Sl-Alex/SmartWatch/FW/hw/src/sm_hw_battery.cpp

/**
    @file sm_hw_battery.cpp
*/
#include "sm_hw_battery.h"

#ifndef PC_SOFTWARE
#include "stm32f10x.h"
#include "sm_hal_gpio.h"

#define GPIO_EN_PORT    GPIOA_BASE  ///< Battery measurement enable port
#define GPIO_EN_PIN     2           ///< Battery measurement enable pin
#define GPIO_ST_PORT    GPIOA_BASE  ///< Charge status port
#define GPIO_ST_PIN     15          ///< Charge status pin
#define MEAS_DELAY      5           ///< Delay between enabling and measurement
#define MEAS_INTERVAL   500         ///< Battery voltage update interval

#define GPIO_AIN_PORT   GPIOA_BASE  ///< Battery voltage input port
#define GPIO_AIN_PIN    0           ///< Battery voltage input pin
#endif

#define VREF    3300                ///< ADC Reference voltage (mV)
#define VOLT_MAX 4100               ///< Maximum battery voltage
#define VOLT_MIN 3500               ///< Minimum battery voltage

#define BAT_MAX ((VOLT_MAX/2)*4096/VREF)    ///< Maximum raw ADC battery voltage
#define BAT_MIN ((VOLT_MIN/2)*4096/VREF)    ///< Minimum raw ADC battery voltage

void SmHwBattery::init()
{
    mRaw = 0;

#ifndef PC_SOFTWARE
    mGpioEn = new SmHalGpio<GPIO_EN_PORT, GPIO_EN_PIN>();
    mGpioEn->setModeSpeed(SM_HAL_GPIO_MODE_OUT_PP, SM_HAL_GPIO_SPEED_2M);
    mGpioEn->setPin();

    // When the charge is
    // in progress this pin is pulled low instead at the end of the charge cycle, a weak pull down of
    // approximately 20µA is connected to the CHRG pin, indicating a present supply power; if the
    // flag is forced high impedance an under voltage condition is detected.
    mGpioStatus = new SmHalGpio<GPIO_ST_PORT, GPIO_ST_PIN>();
    mGpioStatus->setModeSpeed(SM_HAL_GPIO_MODE_IN_PU, SM_HAL_GPIO_SPEED_2M);

    SmHalGpio<GPIO_AIN_PORT, GPIO_AIN_PIN> BatGpio;
    BatGpio.setModeSpeed(SM_HAL_GPIO_MODE_AIN, SM_HAL_GPIO_SPEED_2M);

    ADC1->SQR3 = 0;

    ADC1->CR2 = ADC_CR2_EXTSEL_0 | ADC_CR2_EXTSEL_1 | ADC_CR2_EXTSEL_2 | ADC_CR2_EXTTRIG;

    ADC1->CR2 |= ADC_CR2_ADON;

    // Wait a bit before ADC calibration
    uint32_t timestamp = SmHalSysTimer::getTimeStamp();
    timestamp += MEAS_DELAY;    // 2ms
    // Wait a bit before proceed
    while (SmHalSysTimer::getTimeStamp() <= timestamp);

    ADC1->CR2 |= ADC_CR2_RSTCAL;
    while ((ADC1->CR2 & ADC_CR2_RSTCAL) == ADC_CR2_RSTCAL)
    {
    }

    ADC1->CR2 |= ADC_CR2_CAL;
    while ((ADC1->CR2 & ADC_CR2_RSTCAL) == ADC_CR2_CAL)
    {
    }

    // Enable interrupts
    ADC1->CR1 |= ADC_CR1_EOCIE;
    NVIC_EnableIRQ(ADC1_2_IRQn);

    // Start measurement
    ADC1->CR2 |= ADC_CR2_SWSTART;

    SmHwPowerMgr::getInstance()->subscribe(this);

    mMeasStep = 0;
    SmHalSysTimer::subscribe(this,1,false);
#endif
#ifdef PC_SOFTWARE
    mRaw = 2544;
    SmHalSysTimer::subscribe(this,100,true);
#endif
}

void SmHwBattery::onTimer(uint32_t)
{
#ifndef PC_SOFTWARE
    if (mMeasStep == 0)
    {
        if (mGpioStatus->readPin())
        {
            mCharging = false;
        }
        else
        {
            mCharging = true;
        }
        mGpioStatus->setModeSpeed(SM_HAL_GPIO_MODE_IN_FLOAT, SM_HAL_GPIO_SPEED_2M);
        mGpioEn->setPin();
        SmHalSysTimer::subscribe(this, MEAS_DELAY, false);
        mMeasStep = 1;
    }
    else
    {
        if (mGpioStatus->readPin())
        {
            mChargerConnected = false;
        }
        else
        {
            mChargerConnected = true;
        }
        //mGpioStatus->setModeSpeed(SM_HAL_GPIO_MODE_OUT_PP, SM_HAL_GPIO_SPEED_2M);
        mGpioStatus->setPin();
        mGpioStatus->setModeSpeed(SM_HAL_GPIO_MODE_IN_PU, SM_HAL_GPIO_SPEED_2M);
        mMeasStep = 0;
        ADC1->CR2 |= ADC_CR2_SWSTART;
    }
#else
    updateValues();
#endif
}

#ifndef PC_SOFTWARE
void SmHwBattery::onSleep(void)
{
    ADC1->CR2 &= ~ADC_CR2_ADON;
    mGpioEn->resetPin();
}

void SmHwBattery::onWake(uint32_t wakeSource)
{
    ADC1->CR2 |= ADC_CR2_ADON;
    mMeasStep = 0;
    onTimer(0);
}

extern "C"
{

/// @brief ADC interrupt handler.
/// Measurement enable circuit is disabled after the measurement.
void ADC1_2_IRQHandler (void)
{
    static uint8_t cnt = 3;
    SmHwBattery::getInstance()->mRaw += ADC1->DR;
    SmHwBattery::getInstance()->mGpioEn->resetPin();
    SmHalSysTimer::subscribe(SmHwBattery::getInstance(), MEAS_INTERVAL, false);
    if (--cnt == 0)
    {
        cnt = 3;

        SmHwBattery::getInstance()->mRaw /= 3;

        SmHwBattery::getInstance()->updateValues();
        SmHwBattery::getInstance()->mRaw = 0;
        //SmHwBattery::getInstance()->mGpioStatus->setModeSpeed(SM_HAL_GPIO_MODE_IN_PU, SM_HAL_GPIO_SPEED_2M);
    }
}

}
#endif

void SmHwBattery::updateValues(void)
{
#ifndef PC_SOFTWARE
    if (!mChargerConnected)
    {
        mStatus = BATT_STATUS_DISCHARGING;
    }
    else if (mCharging)
    {
        mStatus = BATT_STATUS_CHARGING;
    }
    else
    {
        mStatus = BATT_STATUS_CHARGED;
    }
#endif
#ifdef PC_SOFTWARE
    mRaw -= 10;
    if (mRaw < BAT_MIN)
    {
        mRaw = BAT_MAX;
        if (mStatus != BATT_STATUS_CHARGING)
        {
            mStatus = (BatteryStatus)((int)mStatus + 1);
        }
        else
        {
            mStatus = (BatteryStatus)0;
        }
    }
#endif

    if (mRaw > BAT_MAX) mRaw = BAT_MAX;
	if (mRaw < BAT_MIN) mRaw = BAT_MIN;

    mCharge = (mRaw - BAT_MIN)*100/(BAT_MAX - BAT_MIN);
	mVoltage = VOLT_MIN + (mRaw - BAT_MIN)*(VOLT_MAX - VOLT_MIN)/(BAT_MAX - BAT_MIN);
}
