Sl-Alex/SmartWatch/FW/hal/inc/sm_hal_abstract_gpio.h

#ifndef SM_HAL_ABSTRACT_GPIO_H
#define SM_HAL_ABSTRACT_GPIO_H

#include "stm32f10x.h"

/// @brief GPIO speed enumeration
enum GpioSpeed
{
    SM_HAL_GPIO_SPEED_10M = 1,  ///< 10MHz maximum
    SM_HAL_GPIO_SPEED_2M,       ///< 2MHz maximum
    SM_HAL_GPIO_SPEED_50M       ///< 50MHz maximum
};

/// @brief Available GPIO modes 
enum GpioMode
{
    SM_HAL_GPIO_MODE_AIN      = 0,      ///< Analog input (useful for ADC inputs)
    SM_HAL_GPIO_MODE_IN_FLOAT = 0x04,   ///< Input without pull-up/down resistors
    SM_HAL_GPIO_MODE_IN_PD    = 0x28,   ///< Input with pull-down resistor
    SM_HAL_GPIO_MODE_IN_PU    = 0x48,   ///< Input with pull-up resistor
    SM_HAL_GPIO_MODE_OUT_OD   = 0x14,   ///< Generic output with open-drain driver
    SM_HAL_GPIO_MODE_OUT_PP   = 0x10,   ///< Generic output with push-pull driver
    SM_HAL_GPIO_MODE_AF_OD    = 0x1C,   ///< Alternative function output with open-drain driver
    SM_HAL_GPIO_MODE_AF_PP    = 0x18    ///< Alternative function output with push-pull driver
};

/// @brief GPIO abstraction
class SmHalAbstractGpio
{
public:

    /// @brief Default constructor
    /// Default pin mode will be set to @ref SM_HAL_GPIO_MODE_IN_FLOAT,
    /// default speed will be limited to @ref SM_HAL_GPIO_SPEED_2M
    SmHalAbstractGpio()
        :mMode(SM_HAL_GPIO_MODE_IN_FLOAT),
        mSpeed(SM_HAL_GPIO_SPEED_2M)
    {}

    /// @brief Set both GPIO mode and speed
    virtual void setModeSpeed(GpioMode mode, GpioSpeed speed) = 0;

    /// @brief Set GPIO mode
    virtual void setMode(GpioMode mode)
    {
        mMode = mode;
        setModeSpeed(mMode, mSpeed);
    }

    /// @brief set GPIO speed
    virtual void setSpeed(GpioSpeed speed)
    {
        mSpeed = speed;
        setModeSpeed(mMode, mSpeed);
    }

    /// @brief Set pin
    virtual void setPin(void) = 0;
    /// @brief Reset pin
    virtual void resetPin(void) = 0;
    /// @brief Read pin state
    virtual uint8_t readPin(void) = 0;

private:
    GpioMode mMode;
    GpioSpeed mSpeed;
};

#endif // SM_HAL_ABSTRACT_GPIO_H
