Sl-Alex/SmartWatch/FW/hal/inc/sm_hal_abstract_spi.h

#ifndef SM_HAL_ABSTRACT_SPI_H
#define SM_HAL_ABSTRACT_SPI_H

/// @file

#include <cstdint>
#include "sm_hal_abstract_gpio.h"

/// @enum SPI configuration
enum SpiConfig {
    SM_HAL_SPI_CFG_FULL_DUPLEX = 0x0000,    ///< Full duplex
    SM_HAL_SPI_CFG_OUT         = 0xC000     ///< Output only
};

/// @brief SPI width
enum SpiWidth {
    SM_HAL_SPI_WIDTH_8  = 0x0000,   ///< 8 bits
    SM_HAL_SPI_WIDTH_16 = 0x0800    ///< 16 bits
};

/// @brief SPI mode (CPOL and CPHA combination)
enum SpiMode {
    SM_HAL_SPI_MODE0 = 0,  ///< CPOL = 0, CPHA = 0 (default low, first edge)
    SM_HAL_SPI_MODE1 = 1,  ///< CPOL = 0, CPHA = 1 (default low, second edge)
    SM_HAL_SPI_MODE2 = 2,  ///< CPOL = 1, CPHA = 0 (default hight, first edge)
    SM_HAL_SPI_MODE3 = 3   ///< CPOL = 1, CPHA = 1 (default hight, second edge)
};

/// @brief SPI Master/Slave mode
enum SpiMsMode {
    SPI_HAL_SPI_MSMODE_MASTER = 0x0104, ///< SPI master
    SPI_HAL_SPI_MSMODE_SLAVE = 0x0000   ///< SPI slave
};

/// @brief SPI nSS pin mode
enum SpiNssMode {
    SPI_HAL_SPI_NSS_MODE_SOFT = 0x0200, ///< Software-controlled nSS pin
    SPI_HAL_SPI_NSS_MODE_HARD = 0x0000  ///< Hardware-controlled nSS pin
};

/// @brief SPI HW abstraction
class SmHalAbstractSpi
{
public:
    /// @brief Constructor
    SmHalAbstractSpi()
        :mSsPin(0)
    {}
    /// @brief SPI transfer
    /// @param in: Input pointer
    /// @param out: Output pointer
    /// @param size: transfer size in bytes
    virtual void transfer(void * in, void * out, int size) = 0;

    /// @brief SPI initialization
    virtual void init(void)
    {
        mSsPin->setModeSpeed(SM_HAL_GPIO_MODE_OUT_PP, SM_HAL_GPIO_SPEED_50M);
        mSsPin->setPin();
    }

    /// @brief SPI deinitialization
    virtual void deInit(void)
    {
        mSsPin->setModeSpeed(SM_HAL_GPIO_MODE_IN_FLOAT, SM_HAL_GPIO_SPEED_50M);
        mSsPin->resetPin();
    }

    /// @brief Destructor
    virtual ~SmHalAbstractSpi() {};

    /// @brief Assign SS pin. It will be high (unselected) by default
    virtual void setSsPin(SmHalAbstractGpio *pSs)
    {
        mSsPin = pSs;
        init();
    }

    /// @brief Set SS pin to high (deselect slave)
    virtual void setSs(void)
    {
        mSsPin->setPin();
    }

    /// @brief Set SS pin to low (select slave)
    virtual void resetSs(void)
    {
        mSsPin->resetPin();
    }

private:
    SmHalAbstractGpio *mSsPin;
};

#endif // SM_HAL_ABSTRACT_SPI_H
